Giuli31/Smart-Glasses-for-Gait-Analysis-/Firmware/PSOC5_Firmware.cydsn/Initialization.h

/* ========================================
 *
 * Copyright YOUR COMPANY, THE YEAR
 * All Rights Reserved
 * UNPUBLISHED, LICENSED SOFTWARE.
 *
 * CONFIDENTIAL AND PROPRIETARY INFORMATION
 * WHICH IS THE PROPERTY OF your company.
 *
 * ========================================
*/
#ifndef __INITIALIZATION_H
    #define __INITIALIZATION_H
    
    #include "cytypes.h"
    #include "stdio.h" 

    // Initialize LEDs
    void INIT_LEDs();
    // check LIS3DH connection
    void CHECK_LIS3DH();
    // Initialize LIS3DH
    void INIT_LIS3DH();
    
#endif
/* [] END OF FILE */
