Giuli31/Smart-Glasses-for-Gait-Analysis-/Firmware/src_shared/LIS3DH.h

/* ========================================
 *
 * Copyright YOUR COMPANY, THE YEAR
 * All Rights Reserved
 * UNPUBLISHED, LICENSED SOFTWARE.
 *
 * CONFIDENTIAL AND PROPRIETARY INFORMATION
 * WHICH IS THE PROPERTY OF your company.
 *
 * ========================================
*/

#ifndef __LIS3DH_H
    #define __LIS3DH_H

    /**
    *   \brief 7-bit I2C address of the slave device.
    */
    #define LIS3DH_DEVICE_ADDRESS 0x18

    /**
    *   \brief Address of the WHO AM I register
    */
    #define LIS3DH_WHO_AM_I_REG_ADDR 0x0F
    
    /**
    *   \brief WHOAMI return value
    */
    #define LIS3DH_WHOAMI_RETVAL     0x33

    /**
    *   \brief Address of the Status register
    */
    #define LIS3DH_STATUS_REG 0x27

    /**
    *   \brief Address of the Control register 1
    */
    #define LIS3DH_CTRL_REG1 0x20

    /**
    *   \brief Hex value to set normal mode to the accelerator
    */
    #define LIS3DH_NORMAL_MODE_CTRL_REG1 0x47
    
    /**
    *   \brief Hex value to set normal mode (powered off)
    **/
    #define LIS3DH_NORMAL_MODE_OFF_CTRL_REG1 0x07

    /**
    *   \brief  Address of the Temperature Sensor Configuration register
    */
    #define LIS3DH_TEMP_CFG_REG 0x1F 

    #define LIS3DH_TEMP_CFG_REG_ACTIVE 0xC0
   
    /////////////////////////////////////////////////
    //EX.3
    
    // Brief Address of CTRL REG 4
    #define LIS3DH_CTRL_REG4 0x23
        
    // brief Block Data Update (BDU) Flag
    
    #define LIS3DH_CTRL_REG4_BDU_ACTIVE 0x80

    // Brief Address of the ADC output LSB register
    
    #define LIS3DH_OUT_ADC_3L 0x0C

    // Brief Address of the ADC output MSB register
    
    #define LIS3DH_OUT_ADC_3H 0x0D
    
    // LSB X output
    #define LIS3DH_OUT_X_L 0x28
    
    // MSB X output
    #define LIS3DH_OUT_X_H 0x29
    
    // CTRL_REG5    
    #define LIS3DH__CTRL_REG5 0x24
    
    //FIFO CTRL REG
    #define LIS3DH__FIFO_CTRL_REG 0x2E
    
    //FIFO SRC REG
    #define LIS3DH__FIFO_SRC_REG 0x2F
    //FIFO CTRL REG 3
    #define LIS3DH_FIFO_CTRL_REG3 0x22
    //Control register 0
     #define LIS3DH_CTRL_REG0 0x1E
    ////////////////////////////////////////////////
    
#endif


/* [] END OF FILE */
